Gymnast544/DS-Input-Interface-Hardware/DS Input Capture KiCAD V1.2/.svg2shenzhen-cache/images/B.Cu_g2419.png

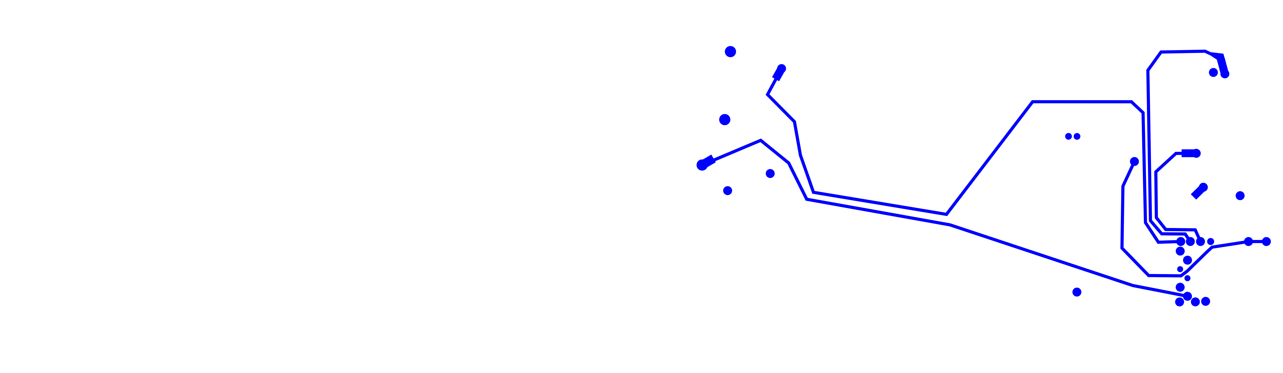
DS Input Capture KiCAD V1.2/.svg2shenzhen-cache/images/B.Cu_g2419.png
