Gymnast544/DS-Input-Interface-Hardware/DS Input Capture KiCAD V1.2/.svg2shenzhen-cache/images/F.Mask_layer4.png

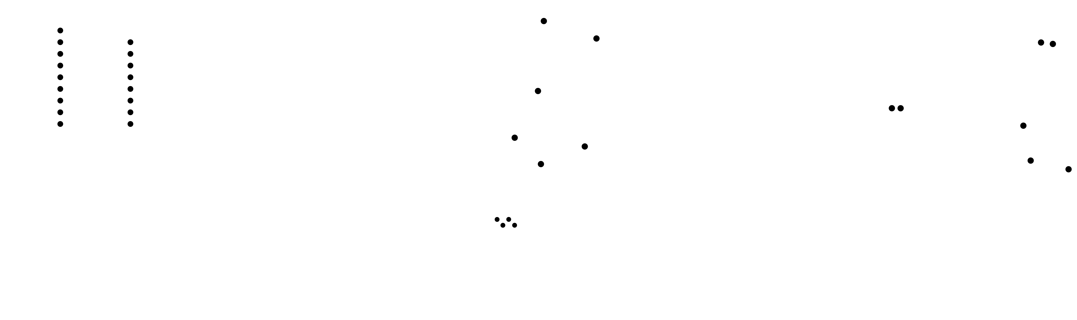
DS Input Capture KiCAD V1.2/.svg2shenzhen-cache/images/F.Mask_layer4.png
