Gymnast544/DS-Input-Interface-Hardware/DS Input Capture KiCAD V1.2/.svg2shenzhen-cache/images/F.Silk_layer2.png

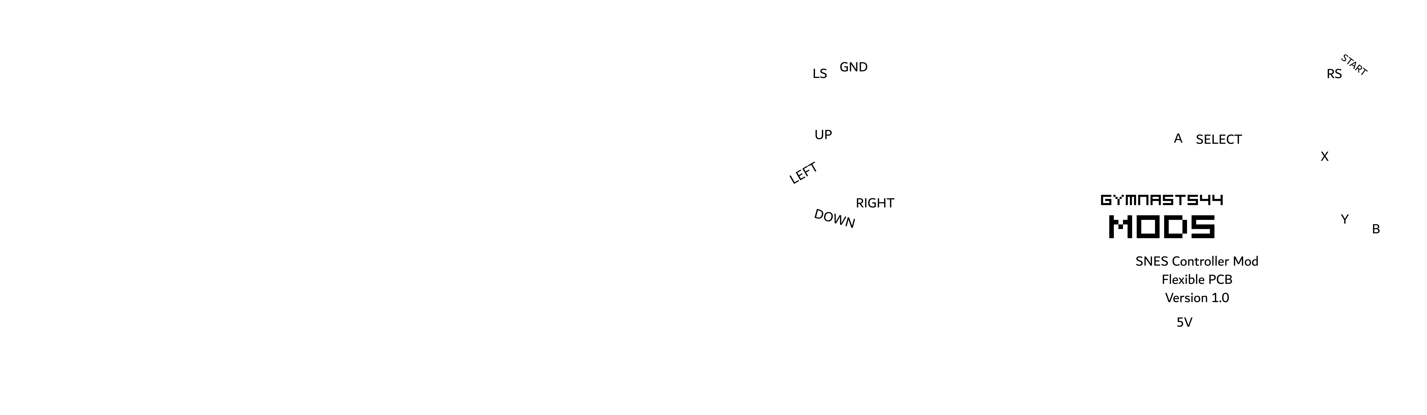
DS Input Capture KiCAD V1.2/.svg2shenzhen-cache/images/F.Silk_layer2.png
